makervan/synthiboard/firmware/r2r_drum_machine_pwm/r2r_drum_machine_pwm.ino

// Arduino Drum Machine
// https://little-scale.blogspot.de/2013/05/diy-polyphonic-drum-machine-and-rhythm.html
// Ported over to Arduino
//
// R2R Reference: http://little-scale.blogspot.com.au/2013/05/teensy-basics-6-r2r-dac-primer.html
//
//
//                             D0   D1   RST
//              GND  GND  VCC  RX   TX   /DTR
//                +--------------------------------+
//                |  [ ]  [ ]  [ ]  [ ]  [ ]  [ ]  |
//                |              FTDI              |
//            D1  | [ ]1/TX                 RAW[ ] |    
//            D0  | [ ]0/RX                 GND[ ] |    
//                | [ ]RST        SCL/A5[ ] RST[ ] |   C6
// GND            | [ ]GND        SDA/A4[ ] VCC[ ] |          - VCC
//.           D2  | [ ]2/INT0    ___         A3[ ] |   C3
// Audio      D3  |~[ ]3/INT1   /   \        A2[ ] |   C2
//            D4  | [ ]4       /PRO  \       A1[ ] |   C1
//            D5  |~[ ]5       \ MINI/       A0[ ] |   C0     - 10k Pot
//            D6  |~[ ]6        \___/    SCK/13[ ] |   B5     - LED
//            D7  | [ ]7          A7[ ] MISO/12[ ] |   B4     - Button 4
//            B0  | [ ]8          A6[ ] MOSI/11[ ]~|   B3     - Button 3
// Button 1 - B1  |~[ ]9                  SS/10[ ]~|   B2     - Button 2
//                |           [RST-BTN]            |    
//                +--------------------------------+  
//   Source:  http://busyducks.com/ascii-art-arduinos
//
//                    +10µF 
//PIN 03 ---[ 1k ]--+---||--->> Audio out
//                  |
//                 === 10nF
//                  |
//                 GND
//https://github.com/dzlonline/the_synth/blob/master/the_synth/examples/modulation/modulation.ino

const byte sound[] PROGMEM = {
    31, 31, 31, 29, 27, 35, 49, 37, 10, 11, 21, 32, 46, 47, 46, 38, 29, 21, 16, 17, 19, 25, 31, 37, 41, 43, 41, 37, 32, 25, 18, 12, 7, 4, 4, 5, 9, 15, 21, 28, 35, 42, 49, 54, 57, 60, 62, 62, 60, 55, 57, 60, 58, 55, 49, 44, 41, 38, 39, 39, 39, 39, 38, 36, 33, 30, 26, 24, 21, 20, 19, 20, 20, 22, 22, 24, 24, 24, 24, 23, 22, 20, 18, 16, 14, 13, 11, 9, 8, 8, 7, 7, 7, 8, 8, 9, 10, 11, 12, 13, 14, 15, 17, 18, 19, 20, 21, 23, 24, 25, 26, 27, 29, 30, 31, 32, 33, 34, 35, 36, 37, 38, 38, 39, 40, 40, 41, 41, 42, 42, 42, 42, 43, 43, 43, 43, 42, 42, 42, 42, 42, 41, 41, 40, 40, 39, 39, 38, 38, 37, 36, 36, 35, 34, 34, 33, 32, 31, 31, 30, 29, 29, 28, 27, 27, 26, 26, 25, 25, 24, 23, 22, 22, 21, 20, 20, 20, 20, 20, 20, 20, 21, 21, 22, 22, 23, 24, 24, 25, 25, 26, 26, 27, 27, 28, 28, 29, 29, 30, 30, 31, 31, 31, 32, 32, 32, 32, 33, 33, 33, 34, 34, 34, 34, 35, 35, 36, 36, 36, 37, 37, 38, 38, 38, 39, 39, 40, 40, 41, 41, 41, 42, 42, 43, 43, 43, 44, 44, 44, 45, 45, 45, 46, 46, 46, 46, 46, 46, 46, 47, 47, 47, 47, 47, 47, 47, 47, 46, 46, 46, 46, 46, 46, 46, 46, 45, 45, 45, 44, 44, 44, 44, 44, 44, 43, 43, 42, 41, 40, 39, 38, 37, 35, 34, 33, 32, 30, 29, 28, 27, 26, 25, 24, 23, 22, 21, 20, 19, 18, 17, 16, 15, 15, 14, 13, 13, 12, 11, 11, 10, 9, 9, 8, 8, 7, 7, 6, 6, 5, 5, 4, 4, 4, 3, 3, 3, 2, 2, 2, 2, 1, 1, 1, 1, 1, 0, 0, 0, 0, 0, 0, 0, 0, 0, 0, 0, 0, 0, 0, 0, 0, 0, 0, 0, 0, 0, 0, 0, 0, 0, 0, 0, 0, 0, 0, 0, 0, 0, 0, 0, 0, 1, 1, 1, 1, 1, 1, 1, 1, 2, 2, 2, 2, 2, 3, 3, 3, 3, 4, 4, 4, 4, 5, 5, 5, 6, 6, 6, 7, 7, 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

void loop() {
  // takte = (analogRead(1) >> 6) + 1;
  for(int j = 0; j < takte; j ++) {
    
    // start playing a subdivsion
    // blink LED
    digitalWrite(13, 3 - (j % 4));
    
    // get pot value and set sampling rate for sample playback
    int sample_rate = (analogRead(0) >> 3) + 2;

    int crush = 1;//(analogRead(1) >> 5) + 1;
  
    takte = 16;//(analogRead(1) >> 6) + 1; 
    
    // read buttons
    for(int k = 0; k < 4; k ++) {
      byte button_data = digitalRead(k + 4); 
      if(button_data != button_previous[k]) {
        button_previous[k] = button_data;
        if(button_data == 0) {
        sound_pattern[k * 16 + j] = 1;
        }
      }
    }
    
    // sample_playback
    for(int i = 0; i < 5000; i+= crush ) {
      // get sample data 
      byte data_1 = sound_pattern[j + 0] * pgm_read_byte_near(sound + i + 0); 
      byte data_2 = sound_pattern[j + 16] * pgm_read_byte_near(sound + i + 5000); 
      byte data_3 = sound_pattern[j + 32] * pgm_read_byte_near(sound + i + 10000); 
      byte data_4 = sound_pattern[j + 48] * pgm_read_byte_near(sound + i + 15000); 
      // write sample data to port
      //PORTD = data_1 + data_2 + data_3 + data_4; 
      OCR2B = data_1 + data_2 + data_3 + data_4;
      delayMicroseconds(sample_rate);
      
    }
  }
}
